rubberducky-png/keyboard1/firmware/keymap.c

#include QMK_KEYBOARD_H
#include "rn4871.h"

void keyboard_post_init_user(void) {
    rn4871_init();
    rn4871_configure_hid();
}

bool process_record_user(uint16_t keycode, keyrecord_t *record) {
    rn4871_update_key(keycode, record->event.pressed);
    return true; 
}

const uint16_t PROGMEM keymaps[][MATRIX_ROWS][MATRIX_COLS] = {
    [0] = LAYOUT(
        KC_ESC, KC_F1, KC_F2, KC_F3, KC_F4, KC_F5, KC_F6, KC_F7, KC_F8, KC_F9, KC_F10, KC_F11, KC_F12, KC_MUTE,
        KC_GRV, KC_1, KC_2, KC_3, KC_4, KC_5, KC_6, KC_7, KC_8, KC_9, KC_0, KC_MINS, KC_EQL, KC_BSPC, KC_INS,
        KC_TAB, KC_Q, KC_W, KC_E, KC_R, KC_T, KC_Y, KC_U, KC_I, KC_O, KC_P, KC_LBRC, KC_RBRC, KC_BSLS, KC_HOME,
        KC_CAPS, KC_A, KC_S, KC_D, KC_F, KC_G, KC_H, KC_J, KC_K, KC_L, KC_SCLN, KC_QUOT, KC_ENT, KC_PGUP,
        KC_LSFT, KC_Z, KC_X, KC_C, KC_V, KC_B, KC_N, KC_M, KC_COMM, KC_DOT, KC_SLSH, KC_RSFT, KC_UP, KC_PGDN,
        KC_LCTL, KC_LGUI, KC_LALT, KC_SPC, KC_RALT, KC_RGUI, KC_LEFT, KC_DOWN, KC_RGHT
    )
};


bool encoder_update_user(uint8_t index, bool clockwise) {
    if (index == 0) {
        if (clockwise) {
            tap_code(KC_VOLU);
        } else {
            tap_code(KC_VOLD);
        }
    }
    return false;
}
